LAMS-UofU/SAME54-board/firmware/lams-xplained-pro/fatfs.h

#ifndef FATFS_H_
#define FATFS_H_

#ifdef __cplusplus
{
#endif /* __cplusplus */

#include <string.h>	
#include <hal_calendar.h>
#include "ff.h"
#include "diskio.h"

extern struct calendar_descriptor CALENDER_INTERFACE;

void FATFS_CALENDAR_CLOCK_init(void);
void FATFS_CALENDAR_init(void);

DWORD get_fattime(void);

void FATFS_sd_status(void);
void FATFS_write_file(TCHAR*, char*, uint32_t);
void FATFS_print_files(char*);

void FATFS_remove_file(TCHAR*);
void FATFS_rename_file(TCHAR*, TCHAR*);

void FATFS_remove_empty_files(void);
void FATFS_fix_numbering(void);
void FATFS_add_hundred(void);

char* FATFS_fresult_desc(FRESULT);
char* DISKIO_dstatus_desc(DSTATUS);

#ifdef __cplusplus
}
#endif /* __cplusplus */

#endif /* FATFS_H_ */
