LAMS-UofU/SAME54-board/firmware/lams-xplained-pro/lams_sd.h

#ifndef LAMS_SD_H_
#define LAMS_SD_H_

#ifdef __cplusplus
{
#endif /* __cplusplus */
	
void SDMMC_init(void);

void SD_menu(void);

#ifdef __cplusplus
}
#endif /* __cplusplus */

#endif /* LAMS_SD_H_ */
