LAMS-UofU/SAME54-board/firmware/lams-xplained-pro/start.h

#ifndef START_H_
#define START_H_

#ifdef __cplusplus
extern "C" {
#endif

/**
 * Initializes MCU, drivers and middleware in the project
 */
void start_init(void);

#ifdef __cplusplus
}
#endif /* __cplusplus */

#endif /* START_H_ */
