LAMS-UofU/SAME54-board/firmware/lams-xplained-pro/atmel_start.h

#ifndef ATMEL_START_H_INCLUDED
#define ATMEL_START_H_INCLUDED

#ifdef __cplusplus
extern "C" {
#endif

#include "driver_init.h"
#include "stdio_start.h"
#include "sd_mmc_start.h"

/**
 * Initializes MCU, drivers and middleware in the project
 **/
void atmel_start_init(void);

#ifdef __cplusplus
}
#endif
#endif
