LAMS-UofU/SAME54-board/firmware/lams-xplained-pro/eeprom.h

#ifndef EEPROM_H_
#define EEPROM_H_

#ifdef __cplusplus
{
#endif /* __cplusplus */

void EEPROM_init(void);
void EEPROM_menu(void);
void EEPROM_read(void);
void EEPROM_write(void);

#ifdef __cplusplus
}
#endif /* __cplusplus */

#endif /* EEPROM_H_ */
